physicsexpert/Excam/picture/IMG_20251031_203658.jpg

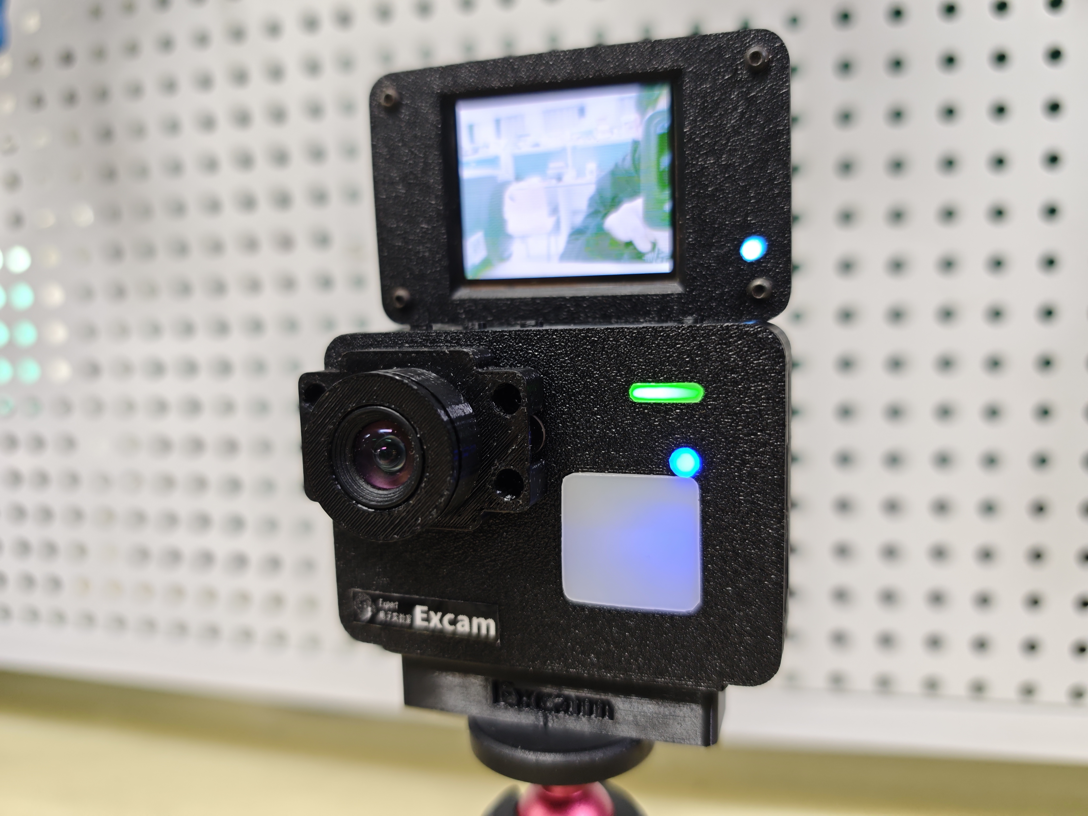
picture/IMG_20251031_203658.jpg
