physicsexpert/Excam/picture/IMG_20251031_203753.jpg

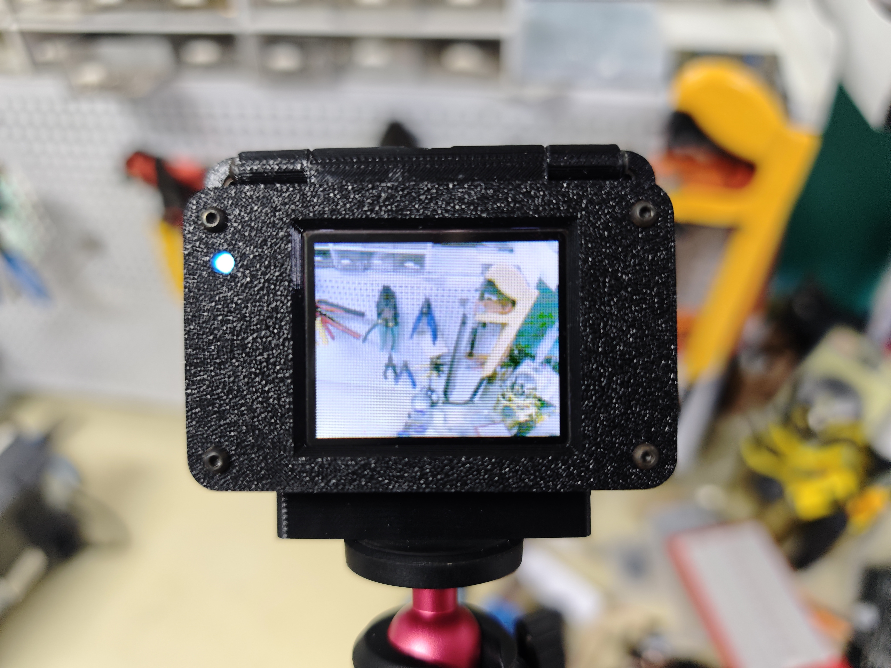
picture/IMG_20251031_203753.jpg
