physicsexpert/Excam/software/代码/视频录制.py

# This work is licensed under the MIT license.
# Copyright (c) 2013-2023 OpenMV LLC. All rights reserved.
# https://github.com/openmv/openmv/blob/master/LICENSE
#
# MJPEG Video Recording Example
#
# Note: You will need an SD card to run this demo.
#
# You can use your OpenMV Cam to record mjpeg files. You can either feed the
# recorder object JPEG frames or RGB565/Grayscale frames. Once you've finished
# recording a Mjpeg file you can use VLC to play it. If you are on Ubuntu then
# the built-in video player will work too.

import sensor
import time
import mjpeg
import machine
import display

lcd = display.SPIDisplay()
sensor.reset()  # Reset and initialize the sensor.
sensor.set_pixformat(sensor.RGB565)  # Set pixel format to RGB565 (or GRAYSCALE)
sensor.set_framesize(sensor.SXGAM)  # Set frame size to QVGA (320x240)
sensor.skip_frames(time=2000)  # Wait for settings take effect.

led = machine.LED("LED_RED")

led.on()
m = mjpeg.Mjpeg("example.mjpeg")

clock = time.clock()  # Create a clock object to track the FPS.
for i in range(200):
    clock.tick()
    m.write(sensor.snapshot())
    print(clock.fps())
    img = sensor.snapshot()
    lcd.write(img)

m.close()
led.off()

raise (Exception("Please reset the camera to see the new file."))
